oselcukyatagan/CLASS_AB_AUDIO_POWER_AMP/LTSpice_Sim_Screenshots/class_ab_audio_power_amp.asc

C2: cap; 1µF
C3: cap; 4700µf
C4: cap; 1µF
C5: cap; 1µF
C6: cap; 4700µf
C7: cap; 1µF
C8: cap; 4700µf
C9: cap; 4700µf
C10: cap; 4700µF
C11: cap; 100pF
C12: cap; 4700µf
C13: cap; 100pF
C14: polcap; 100µF
C15: cap; 0.1µF
C16: cap; 100pF
C17: cap; 10µF
C18: cap; 10µF
C20: polcap; 100µF
C21: cap; 10µF
D1: diode; 1N4148
D2: diode; 1N4007
D3: diode; 1N4007
D4: diode; 1N4148
D5: diode; 1N4007
D6: diode; 1N4007
D7: diode; 1N4148
D8: diode; 1N4148
D9: diode; 1N4148
D10: diode; 1N4148
GUITAR_SIGNAL: voltage; SINE(0 200m 5k 0)
L1: ind; 10; Rser=10
L2: ind; 42.5m; Rser=1
L3: ind; 42.5m; Rser=1
Q1: pnp
Q2: pnp
Q3: npn; 2N3904
Q4: pnp; 2N3906
Q5: npn
Q6: pnp
Q7: npn
Q8: pnp
Q9: npn
Q10: npn
Q11: pnp
Q12: npn; 2N3904
Q13: pnp
R1: res; 100; tol=5
R2: res; 8; tol=5
R3: res; 470; tol=5
R4: res; 10k
R5: res; 220; tol=5
R6: res; 10k
R7: res; 8
R8: res; 1k
R9: res; 0.22; pwr=2
R10: res; 2k
R11: res; 0.2
R12: res; 100; tol=5
R13: res; 0.22; pwr=2
R14: res; 2k
R15: res; 1k
R16: res; 100; tol=5
R17: res; 470; tol=5
R18: res; 10k
R20: res; 9.1k
R21: res; 1k
R27: res; 9.1k; tol=5
R28: res; 47; tol=5 pwr=1
R29: res; 47; tol=5 pwr=1
R30: res; 47; tol=5 pwr=1
R31: res; 47; tol=5 pwr=1
R37: res; 47; tol=5
R38: res; 47; tol=5
V1: voltage; 19
V2: voltage; 19
V4: voltage; SINE(0 325 50 0)
Named nets: 0, out, VCC, VEE, VCC_PSU, VEE_PSU
K. L1 L2 L3 1
.tran 0 5m 0 1u
